AqeelMuhammad/Solar-Charger/Design Files/Enclosure/Battery case lid/Renderings/GameBoyBatteryCover3.JPG

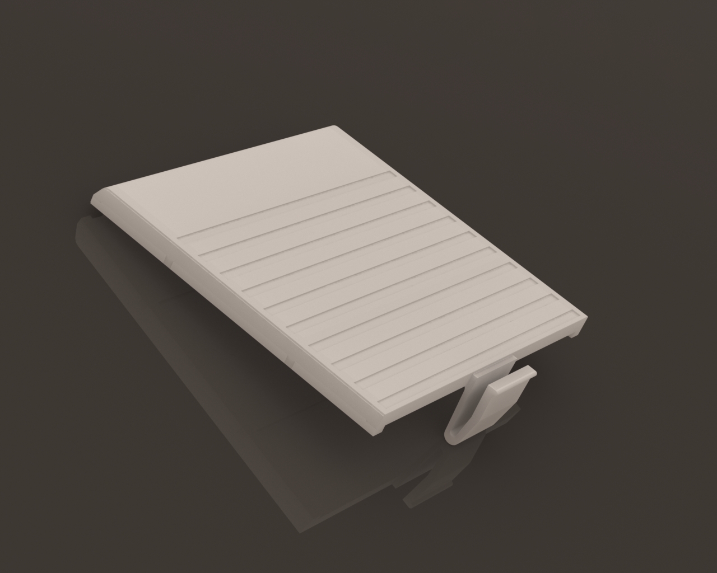
Design Files/Enclosure/Battery case lid/Renderings/GameBoyBatteryCover3.JPG
