AqeelMuhammad/Solar-Charger/Images/EnclosureBack.jpeg

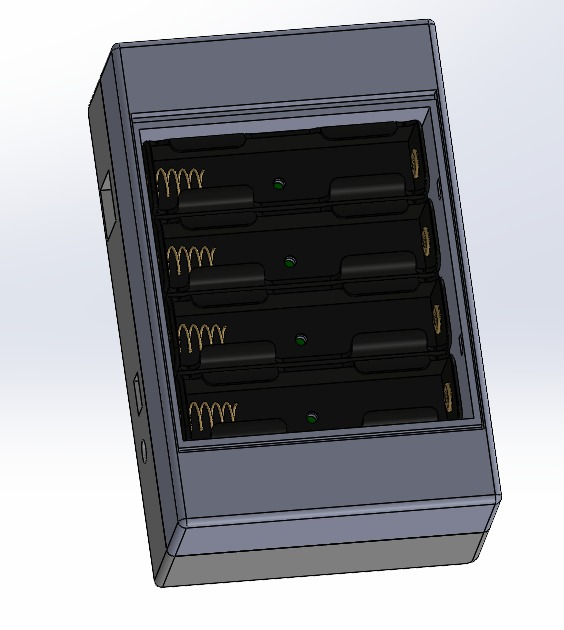
Images/EnclosureBack.jpeg
