AqeelMuhammad/Solar-Charger/Images/EnclosureSide2.jpeg

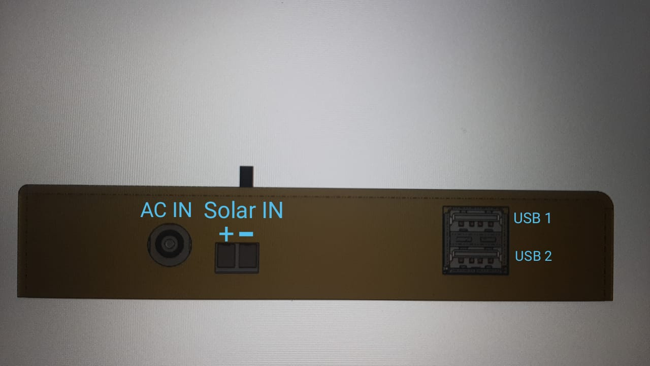
Images/EnclosureSide2.jpeg
