AqeelMuhammad/Solar-Charger/Images/PCB.jpeg

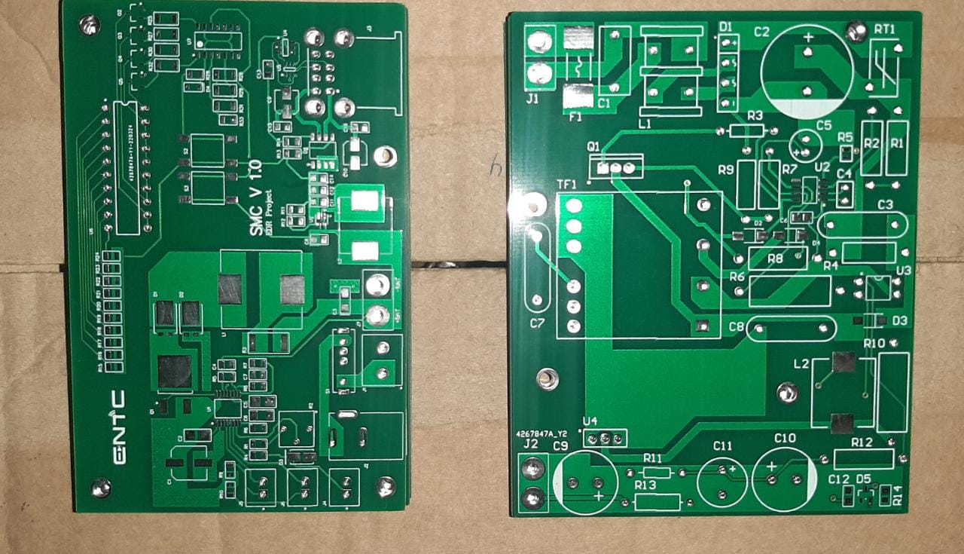
Images/PCB.jpeg
