AqeelMuhammad/Solar-Charger/Images/SubPCB.jpeg

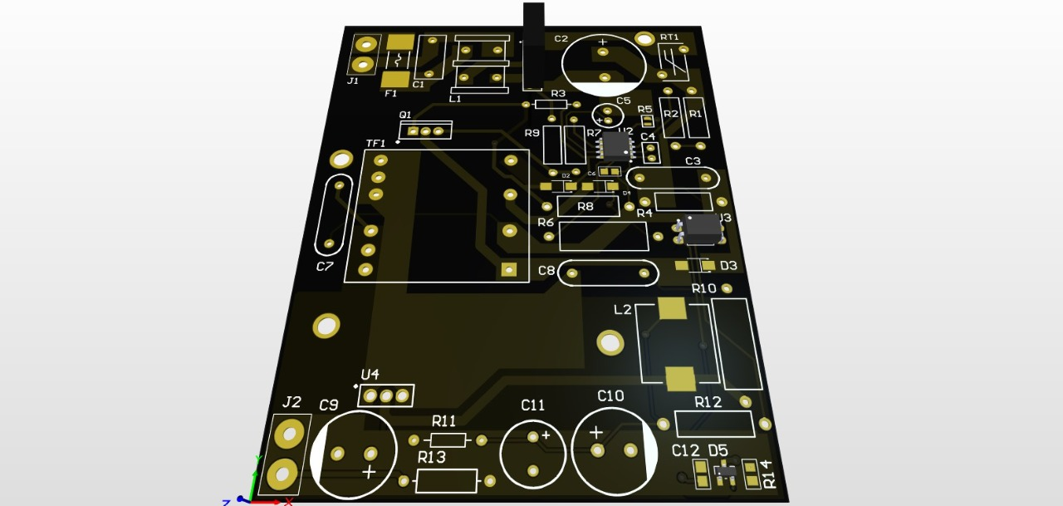
Images/SubPCB.jpeg
